filliformes/pandore/doc/case+inst_v2_front.jpg

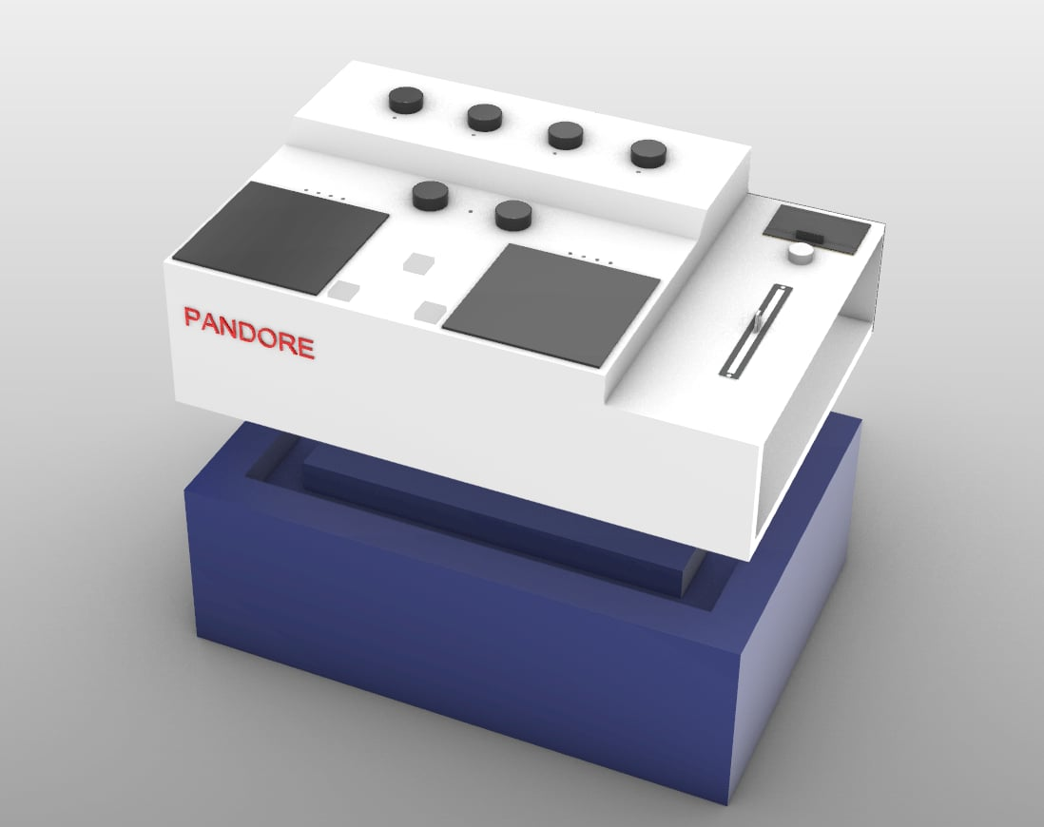
doc/case+inst_v2_front.jpg
