filliformes/pandore/doc/rp2350.kicad_sch

## KiCad design doc/rp2350.kicad_sch (2026-05-19)

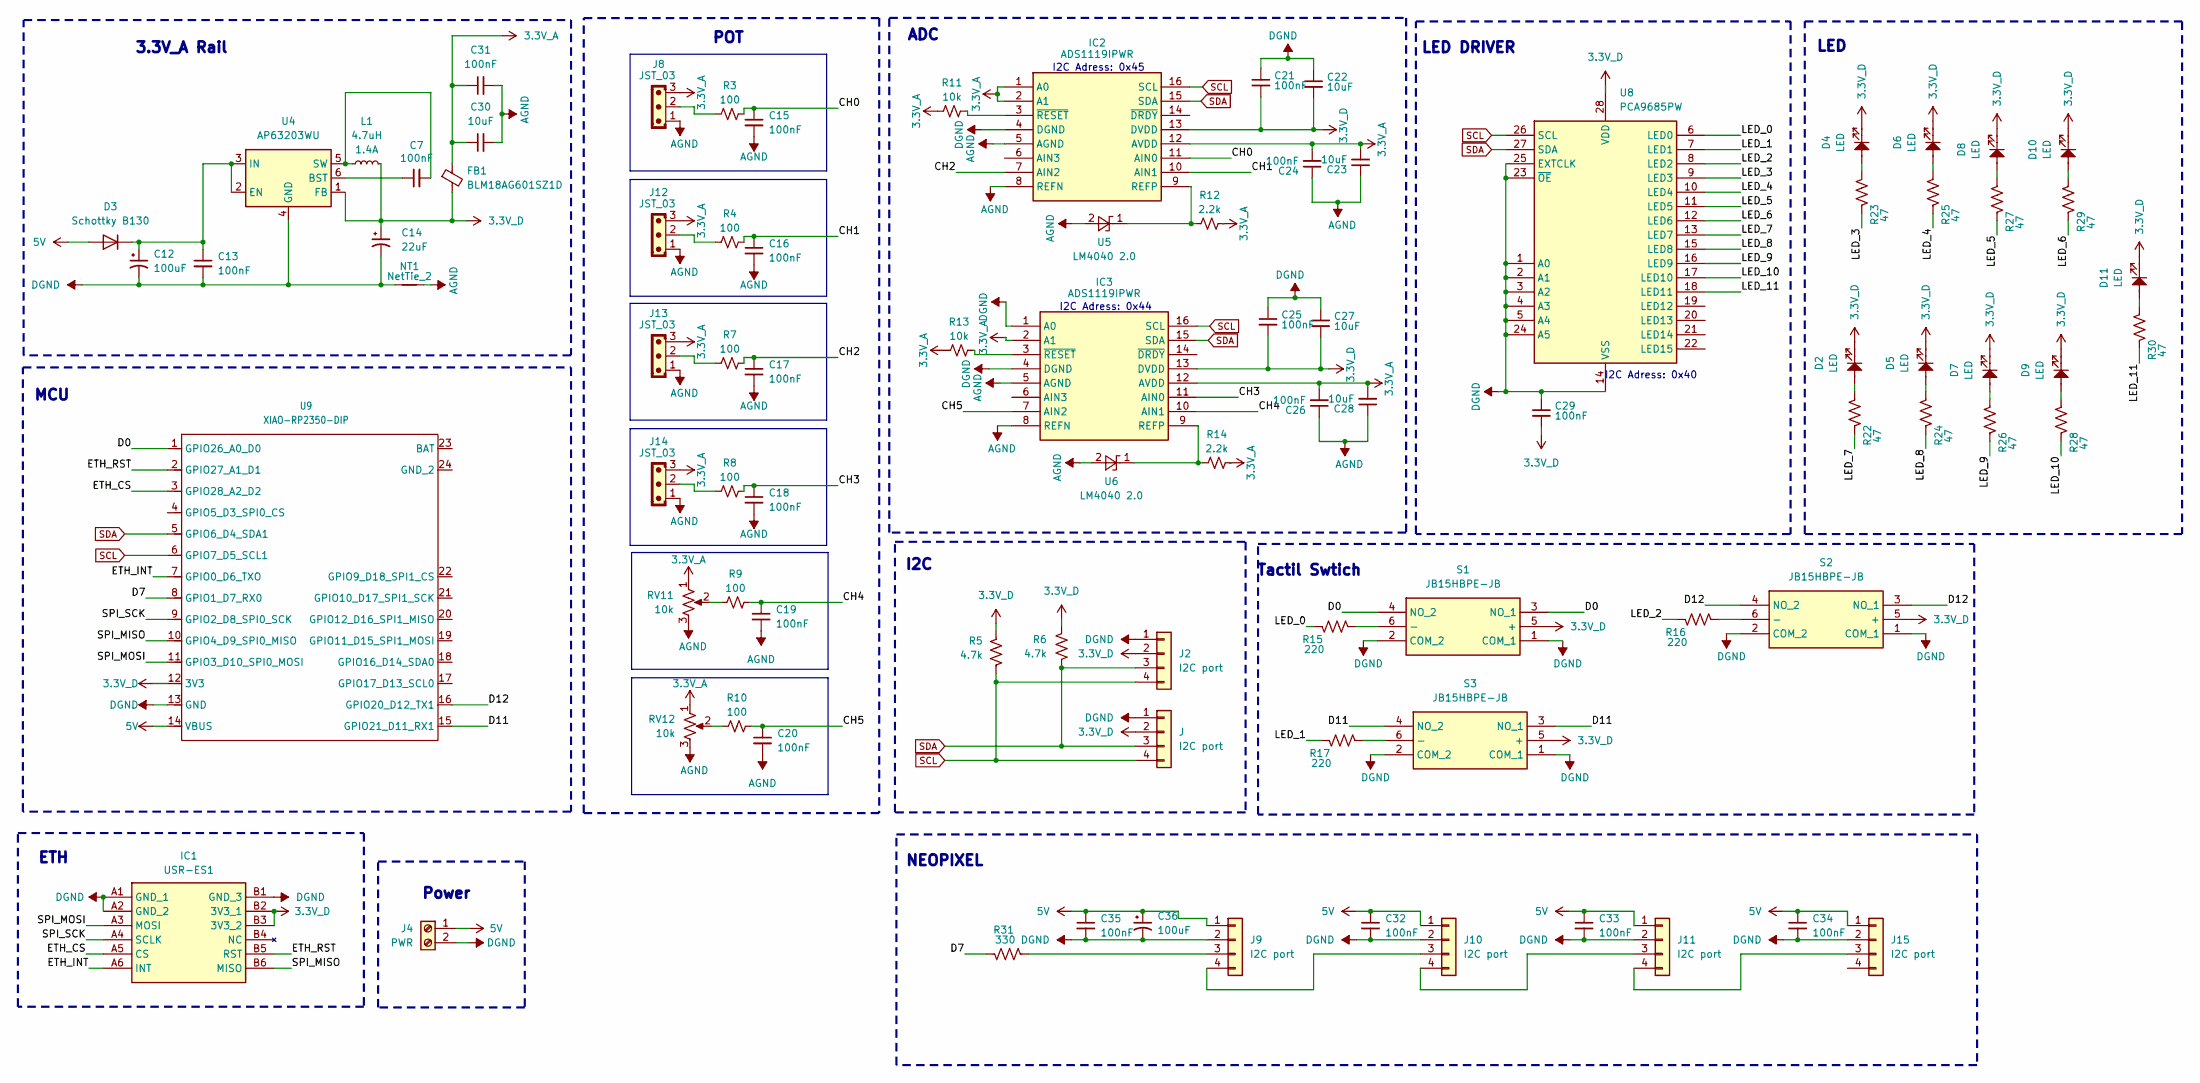
[picture p9: schematic rp2350.kicad_sch]

Parts:
C7: C_Small; C_0603_1608Metric; Voltage 100nF; Tolerance 100%
C12, C36: 100uF
C13, C15, C16, C17, C18, C19, C20, C21, C24, C25, C26, C29, C31, C32, C33, C34, C35: 100nF
C14: 22uF
C22, C23, C27, C28, C30: 10uF
D2, D4, D5, D6, D7, D8, D9, D10, D11: LED; LED_D5.0mm
D3: Schottky B130
FB1: BLM18AG601SZ1D
IC1: USR-ES1; USRES1; Manufacturer_Part_Number USR-ES1
IC2, IC3: ADS1119IPWR; SOP65P640X120-16N; Manufacturer_Part_Number ADS1119IPWR; Mouser Part Number 595-ADS1119IPWR
J, J2, J9, J10, J11, J15: I2C port
J4: PWR
J8, J12, J13, J14: JST_03; JST_EH_B3B-EH-A_1x03_P2.50mm_Vertical
L1: 4.7uH; 1008_2520Metric
NT1: NetTie_2
R3, R4, R7, R8, R9, R10: 100
R5, R6: 4.7k
R11, R13: 10k
R12, R14: 2.2k
R15, R16, R17: 220
R22, R23, R24, R25, R26, R27, R28, R29, R30: 47
R31: 330
RV11, RV12: 10k
S1, S2, S3: JB15HBPE-JB; JB15HBPFJB; Manufacturer_Part_Number JB15HBPE-JB; Mouser Part Number 633-JB15HBPE-JB
U4: AP63203WU; TSOT-23-6
U5, U6: LM4040 2.0; SOT-23
U8: PCA9685PW; TSSOP-28_4.4x9.7mm_P0.65mm
U9: XIAO-RP2350-DIP; PinSocket_2x12_P1.00mm_Vertical_SMD

Connections:
3.3V_A: C23.2, C24.2, C26.2, C28.2, C30.1, C31.1, FB1.1, IC2.1 (A0), IC2.2 (A1), IC2.12 (AVDD), IC3.2 (A1), IC3.12 (AVDD), J8.3, J12.3, J13.3, J14.3, R11.1, R12.2, R13.1, R14.2, RV11.1, RV12.1
3.3V_D: C14.1, C21.2, C22.2, C25.2, C27.2, C29.2, D2.1, D4.1, D5.1, D6.1, D7.1, D8.1, D9.1, D10.1, D11.1, FB1.2, IC1.B2 (3V3_1), IC1.B3 (3V3_2), IC2.13 (DVDD), IC3.13 (DVDD), J.2, J2.2, L1.2, R5.2, R6.2, S1.5 (+), S2.5 (+), S3.5 (+), U4.1 (FB), U8.28 (VDD), U9.12 (3V3)
5V: C32.1, C33.1, C34.1, C35.1, C36.1, D3.2 (A), J4.1, J9.1, J10.1, J11.1, J15.1, U9.14 (VBUS)
AGND: C15.2, C16.2, C17.2, C18.2, C19.2, C20.2, C23.1, C24.1, C26.1, C28.1, C30.2, C31.2, IC2.5 (AGND), IC2.8 (REFN), IC3.5 (AGND), IC3.8 (REFN), J8.1, J12.1, J13.1, J14.1, NT1.2, RV11.3, RV12.3, U5.2 (A), U6.2 (A)
CH0: C15.1, IC2.11 (AIN0), R3.2
CH1: C16.1, IC2.10 (AIN1), R4.2
CH2: C17.1, IC2.7 (AIN2), R7.2
CH3: C18.1, IC3.11 (AIN0), R8.2
CH4: C19.1, IC3.10 (AIN1), R9.2
CH5: C20.1, IC3.7 (AIN2), R10.2
D0: S1.3 (NO_1), S1.4 (NO_2), U9.1 (GPIO26_A0_D0)
D7: R31.2, U9.8 (GPIO1_D7_RX0)
D11: S3.3 (NO_1), S3.4 (NO_2), U9.15 (GPIO21_D11_RX1)
D12: S2.3 (NO_1), S2.4 (NO_2), U9.16 (GPIO20_D12_TX1)
DGND: C12.2, C13.2, C14.2, C21.1, C22.1, C25.1, C27.1, C29.1, C32.2, C33.2, C34.2, C35.2, C36.2, IC1.A1 (GND_1), IC1.A2 (GND_2), IC1.B1 (GND_3), IC2.4 (DGND), IC3.1 (A0), IC3.4 (DGND), J.1, J2.1, J4.2, J9.2, J10.2, J11.2, J15.2, NT1.1, S1.1 (COM_1), S1.2 (COM_2), S2.1 (COM_1), S2.2 (COM_2), S3.1 (COM_1), S3.2 (COM_2), U4.4 (GND), U8.1 (A0), U8.2 (A1), U8.3 (A2), U8.4 (A3), U8.5 (A4), U8.14 (VSS), U8.23 (~OE), U8.24 (A5), U8.25 (EXTCLK), U9.13 (GND)
ETH_CS: IC1.A5 (CS), U9.3 (GPIO28_A2_D2)
ETH_INT: IC1.A6 (INT), U9.7 (GPIO0_D6_TXO)
ETH_RST: IC1.B5 (RST), U9.2 (GPIO27_A1_D1)
LED_0: R15.2, U8.6 (LED0)
LED_1: R17.2, U8.7 (LED1)
LED_2: R16.2, U8.8 (LED2)
LED_3: R23.2, U8.9 (LED3)
LED_4: R25.2, U8.10 (LED4)
LED_5: R27.2, U8.11 (LED5)
LED_6: R29.2, U8.12 (LED6)
LED_7: R22.2, U8.13 (LED7)
LED_8: R24.2, U8.15 (LED8)
LED_9: R26.2, U8.16 (LED9)
LED_10: R28.2, U8.17 (LED10)
LED_11: R30.2, U8.18 (LED11)
unnamed: C7.1, U4.6 (BST)
unnamed: C7.2, L1.1, U4.5 (SW)
unnamed: C12.1, C13.1, D3.1 (K), U4.2 (EN), U4.3 (IN)
unnamed: D2.2, R22.1
unnamed: D4.2, R23.1
unnamed: D5.2, R24.1
unnamed: D6.2, R25.1
unnamed: D7.2, R26.1
unnamed: D8.2, R27.1
unnamed: D9.2, R28.1
unnamed: D10.2, R29.1
unnamed: D11.2, R30.1
unnamed: IC2.3 (~RESET), R11.2
unnamed: IC2.9 (REFP), R12.1, U5.1 (K)
unnamed: IC3.3 (~RESET), R13.2
unnamed: IC3.9 (REFP), R14.1, U6.1 (K)
unnamed: J8.2, R3.1
unnamed: J9.3, R31.1
unnamed: J9.4, J10.3
unnamed: J10.4, J11.3
unnamed: J11.4, J15.3
unnamed: J12.2, R4.1
unnamed: J13.2, R7.1
unnamed: J14.2, R8.1
unnamed: R9.1, RV11.2
unnamed: R10.1, RV12.2
unnamed: R15.1, S1.6 (-)
unnamed: R16.1, S2.6 (-)
unnamed: R17.1, S3.6 (-)
SCL: IC2.16 (SCL), IC3.16 (SCL), J.4, J2.4, R5.1, U8.26 (SCL), U9.6 (GPIO7_D5_SCL1)
SDA: IC2.15 (SDA), IC3.15 (SDA), J.3, J2.3, R6.1, U8.27 (SDA), U9.5 (GPIO6_D4_SDA1)
SPI_MISO: IC1.B6 (MISO), U9.10 (GPIO4_D9_SPI0_MISO)
SPI_MOSI: IC1.A3 (MOSI), U9.11 (GPIO3_D10_SPI0_MOSI)
SPI_SCK: IC1.A4 (SCLK), U9.9 (GPIO2_D8_SPI0_SCK)

Notes on the sheet:
POT
I2C Adress: 0x44
ETH
Power
ADC
Tactil Swtich
LED DRIVER
NEOPIXEL
I2C Adress: 0x40
I2C
3.3V_A Rail
LED
I2C Adress: 0x45
MCU
