filliformes/pandore/hw/pandore-mdot2.kicad_sch

## KiCad design hw/pandore-mdot2.kicad_sch (2026-05-19)

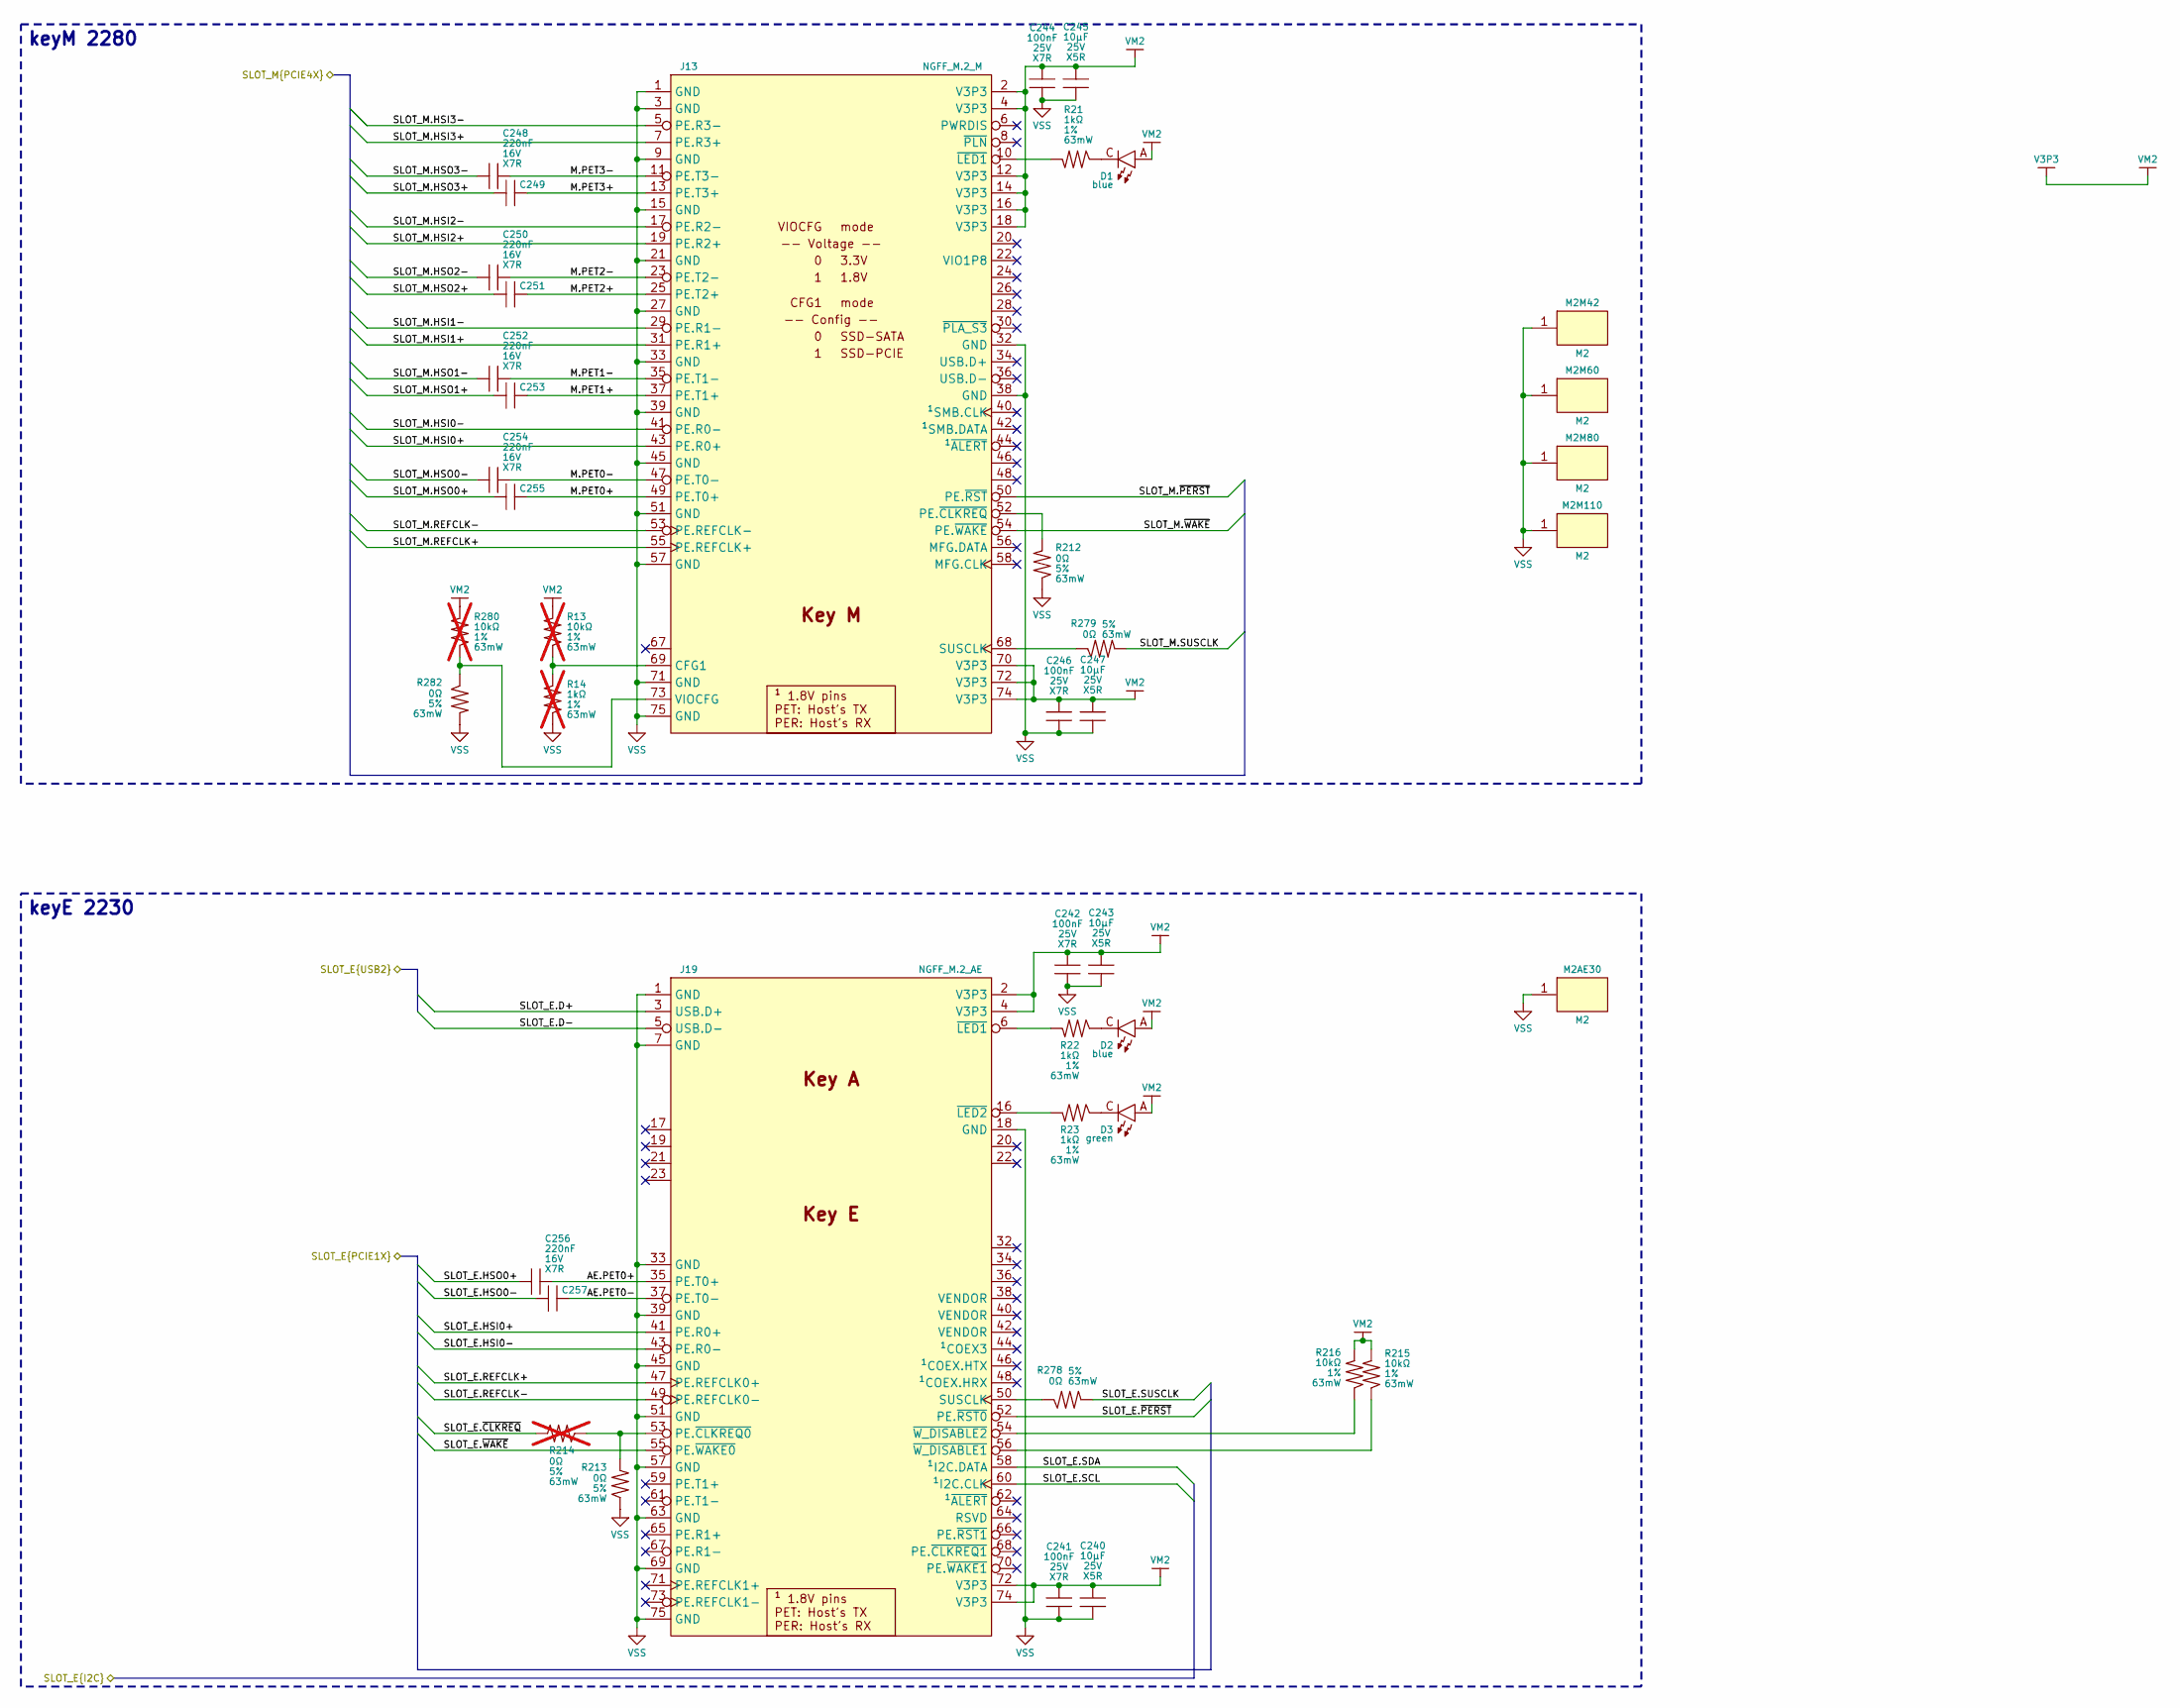
[picture p10: schematic pandore-mdot2.kicad_sch]

Parts:
C240, C243, C245, C247: 10µF, 25V, X5R; CAPC2012; Voltage 25V; MPN GRM21BR61E106KA73K
C241, C242, C244, C246: 100nF, 25V, X7R; CAPC1005; Voltage 25V; MPN 0402B104K160CT
C248, C249, C250, C251, C252, C253, C254, C255, C256, C257: 220nF, 16V, X7R; CAPC1005; Voltage 16V; MPN GRM155R71C224KA12D
D1, D2: blue; LEDM1608X80; MPN KB EELP41.12-P1R2-36-3X4X
D3: green; LEDM1608X80; MPN KT EELP41.12-S2U1-25-2X4Y
J13: NGFF_M.2_M; NGFF_M.2_CONN; MPN 10131758-005RLF
J19: NGFF_M.2_AE; NGFF_M.2_CONN; MPN 2199230-2
M2AE30, M2M42, M2M60, M2M80, M2M110: M2; mnt_M2_ele; MPN MPN
R13, R280: 10kΩ, 1%, 63mW; RESC1005; Tolerance 1%; MPN CR0402-FX-1002GLF; not fitted
R14: 1kΩ, 1%, 63mW; RESC1005; Tolerance 1%; MPN RC0402FR-131KL; not fitted
R21, R22, R23: 1kΩ, 1%, 63mW; RESC1005; Tolerance 1%; MPN RC0402FR-131KL
R212, R213, R278, R279, R282: 0Ω, 5%, 63mW; RESC1005; Tolerance 5%; MPN RC0402JR-070RL
R214: 0Ω, 5%, 63mW; RESC1005; Tolerance 5%; MPN RC0402JR-070RL; not fitted
R215, R216: 10kΩ, 1%, 63mW; RESC1005; Tolerance 1%; MPN CR0402-FX-1002GLF

Connections:
AE.PET0+: C256.1, J19.35 (PE.T0+)
AE.PET0-: C257.1, J19.37 (PE.T0-)
M.PET0+: C255.1, J13.49 (PE.T0+)
M.PET0-: C254.1, J13.47 (PE.T0-)
M.PET1+: C253.1, J13.37 (PE.T1+)
M.PET1-: C252.1, J13.35 (PE.T1-)
M.PET2+: C251.1, J13.25 (PE.T2+)
M.PET2-: C250.1, J13.23 (PE.T2-)
M.PET3+: C249.1, J13.13 (PE.T3+)
M.PET3-: C248.1, J13.11 (PE.T3-)
unnamed: D1.C, R21.2
unnamed: D2.C, R22.2
unnamed: D3.C, R23.2
unnamed: J13.10 (~LED1), R21.1
unnamed: J13.52 (PE.~CLKREQ), R212.1
unnamed: J13.68 (SUSCLK), R279.2
unnamed: J13.69 (CFG1), R13.2, R14.1
unnamed: J13.73 (VIOCFG), R280.2, R282.2
unnamed: J19.6 (~LED1), R22.1
unnamed: J19.16 (~LED2), R23.1
unnamed: J19.50 (SUSCLK), R278.2
unnamed: J19.53 (PE.~CLKREQ0), R213.1, R214.2
unnamed: J19.54 (~W_DISABLE2), R216.2
unnamed: J19.56 (~W_DISABLE1), R215.2
SLOT_E.D+: J19.3 (USB.D+)
SLOT_E.D-: J19.5 (USB.D-)
SLOT_E.HSI0+: J19.41 (PE.R0+)
SLOT_E.HSI0-: J19.43 (PE.R0-)
SLOT_E.HSO0+: C256.2
SLOT_E.HSO0-: C257.2
SLOT_E.REFCLK+: J19.47 (PE.REFCLK0+)
SLOT_E.REFCLK-: J19.49 (PE.REFCLK0-)
SLOT_E.SCL: J19.60 (¹I2C.CLK)
SLOT_E.SDA: J19.58 (¹I2C.DATA)
SLOT_E.SUSCLK: R278.1
SLOT_E.~CLKREQ: R214.1
SLOT_E.~PERST: J19.52 (PE.~RST0)
SLOT_E.~WAKE: J19.55 (PE.~WAKE0)
SLOT_M.HSI0+: J13.43 (PE.R0+)
SLOT_M.HSI0-: J13.41 (PE.R0-)
SLOT_M.HSI1+: J13.31 (PE.R1+)
SLOT_M.HSI1-: J13.29 (PE.R1-)
SLOT_M.HSI2+: J13.19 (PE.R2+)
SLOT_M.HSI2-: J13.17 (PE.R2-)
SLOT_M.HSI3+: J13.7 (PE.R3+)
SLOT_M.HSI3-: J13.5 (PE.R3-)
SLOT_M.HSO0+: C255.2
SLOT_M.HSO0-: C254.2
SLOT_M.HSO1+: C253.2
SLOT_M.HSO1-: C252.2
SLOT_M.HSO2+: C251.2
SLOT_M.HSO2-: C250.2
SLOT_M.HSO3+: C249.2
SLOT_M.HSO3-: C248.2
SLOT_M.REFCLK+: J13.55 (PE.REFCLK+)
SLOT_M.REFCLK-: J13.53 (PE.REFCLK-)
SLOT_M.SUSCLK: R279.1
SLOT_M.~PERST: J13.50 (PE.~RST)
SLOT_M.~WAKE: J13.54 (PE.~WAKE)
V3P3: C240.2, C241.2, C242.2, C243.2, C244.2, C245.2, C246.2, C247.2, D1.A, D2.A, D3.A, J13.2 (V3P3), J13.4 (V3P3), J13.12 (V3P3), J13.14 (V3P3), J13.16 (V3P3), J13.18 (V3P3), J13.70 (V3P3), J13.72 (V3P3), J13.74 (V3P3), J19.2 (V3P3), J19.4 (V3P3), J19.72 (V3P3), J19.74 (V3P3), R13.1, R215.1, R216.1, R280.1
VSS: C240.1, C241.1, C242.1, C243.1, C244.1, C245.1, C246.1, C247.1, J13.1 (GND), J13.3 (GND), J13.9 (GND), J13.15 (GND), J13.21 (GND), J13.27 (GND), J13.32 (GND), J13.33 (GND), J13.38 (GND), J13.39 (GND), J13.45 (GND), J13.51 (GND), J13.57 (GND), J13.71 (GND), J13.75 (GND), J19.1 (GND), J19.7 (GND), J19.18 (GND), J19.33 (GND), J19.39 (GND), J19.45 (GND), J19.51 (GND), J19.57 (GND), J19.63 (GND), J19.69 (GND), J19.75 (GND), M2AE30.1, M2M42.1, M2M60.1, M2M80.1, M2M110.1, R14.2, R212.2, R213.2, R282.1

Notes on the sheet:
keyE 2230
keyM 2280
